JarrettR/USBvil/Firmware/HID/firmware/src/system_config/exp16/dspic33ep256mu506_pim/system.c

/********************************************************************
 Software License Agreement:

 The software supplied herewith by Microchip Technology Incorporated
 (the "Company") for its PIC(R) Microcontroller is intended and
 supplied to you, the Company's customer, for use solely and
 exclusively on Microchip PIC Microcontroller products. The
 software is owned by the Company and/or its supplier, and is
 protected under applicable copyright laws. All rights are reserved.
 Any use in violation of the foregoing restrictions may subject the
 user to criminal sanctions under applicable laws, as well as to
 civil liability for the breach of the terms and conditions of this
 license.

 THIS SOFTWARE IS PROVIDED IN AN "AS IS" CONDITION. NO WARRANTIES,
 WHETHER EXPRESS, IMPLIED OR STATUTORY, INCLUDING, BUT NOT LIMITED
 TO, IMPLIED WARRANTIES OF MERCHANTABILITY AND FITNESS FOR A
 PARTICULAR PURPOSE APPLY TO THIS SOFTWARE. THE COMPANY SHALL NOT,
 IN ANY CIRCUMSTANCES, BE LIABLE FOR SPECIAL, INCIDENTAL OR
 CONSEQUENTIAL DAMAGES, FOR ANY REASON WHATSOEVER.
 *******************************************************************/

#include <p33EP256MU506.h>
#include "system.h"
#include "system_config.h"
#include "usb.h"
#include "leds.h"
#include "buttons.h"
#include "adc.h"

/** CONFIGURATION Bits **********************************************/
// FICD
#pragma config ICS = PGD1               // ICD Communication Channel Select bits (Communicate on PGEC1 and PGED1)
#pragma config JTAGEN = OFF             // JTAG Enable bit (JTAG is disabled)

// FPOR
#pragma config DFMCY = DFMCY_8          // Data Flash Memory Cycle Count (8 Tcy)
#pragma config BOREN = OFF              // Brown Out Reset Enable bit (Brown Out Reset Disabled)
#pragma config ALTI2C1 = OFF            // Alternate I2C1 pins (I2C1 mapped to SDA1/SCL1 pins)
#pragma config ALTI2C2 = OFF            // Alternate I2C2 pins (I2C2 mapped to SDA2/SCL2 pins)
#pragma config WDTWIN = WIN25           // Watchdog Window Select bits (WDT Window is 25% of WDT period)

// FWDT
#pragma config WDTPOST = PS32768        // Watchdog Timer Postscaler bits (1:32,768)
#pragma config WDTPRE = PR128           // Watchdog Timer Prescaler bit (1:128)
#pragma config PLLKEN = ON              // PLL Lock Enable bit (Clock switch to PLL source will wait until the PLL lock signal is valid.)
#pragma config WINDIS = OFF             // Watchdog Timer Window Enable bit (Watchdog Timer in Non-Window mode)
#pragma config FWDTEN = OFF             // Watchdog Timer Enable bit (Watchdog timer enabled/disabled by user software)

// FOSC
#pragma config POSCMD = HS              // Primary Oscillator Mode Select bits (HS Crystal Oscillator Mode)
#pragma config OSCIOFNC = ON            // OSC2 Pin Function bit (OSC2 is general purpose digital I/O pin)
#pragma config IOL1WAY = OFF            // Peripheral pin select configuration (Allow multiple reconfigurations)
#pragma config FCKSM = CSDCMD           // Clock Switching Mode bits (Both Clock switching and Fail-safe Clock Monitor are disabled)

// FOSCSEL
#pragma config FNOSC = PRIPLL           // Oscillator Source Selection (Primary Oscillator with PLL module (XT + PLL, HS + PLL, EC + PLL))
#pragma config PWMLOCK = OFF            // PWM Lock Enable bit (PWM registers may be written without key sequence)
#pragma config IESO = OFF               // Two-speed Oscillator Start-up Enable bit (Start up with user-selected oscillator source)

// FGS
#pragma config GWRP = OFF               // General Segment Write-Protect bit (General Segment may be written)
#pragma config GCP = OFF                // General Segment Code-Protect bit (General Segment Code protect is Disabled)

/*********************************************************************
* Function: void SYSTEM_Initialize( SYSTEM_STATE state )
*
* Overview: Initializes the system.
*
* PreCondition: None
*
* Input:  SYSTEM_STATE - the state to initialize the system into
*
* Output: None
*
********************************************************************/
void SYSTEM_Initialize( SYSTEM_STATE state )
{
    switch(state)
    {
        case SYSTEM_STATE_USB_START:
            ANSELA = 0x0000;
            ANSELB = 0x0000;
            ANSELC = 0x0000;
            ANSELE = 0x0000;
            ANSELG = 0x0000;

            // Configure the device PLL to obtain 60 MIPS operation. The crystal
            // frequency is 8MHz. Divide 8MHz by 2, multiply by 60 and divide by
            // 2. This results in Fosc of 120MHz. The CPU clock frequency is
            // Fcy = Fosc/2 = 60MHz. Wait for the Primary PLL to lock and then
            // configure the auxilliary PLL to provide 48MHz needed for USB
            // Operation.

            PLLFBD = 58;                        /* M  = 60  */
            CLKDIVbits.PLLPOST = 0;             /* N1 = 2   */
            CLKDIVbits.PLLPRE = 0;              /* N2 = 2   */
            OSCTUN = 0;

            /*	Initiate Clock Switch to Primary
             *	Oscillator with PLL (NOSC= 0x3)*/
            __builtin_write_OSCCONH(0x03);
            __builtin_write_OSCCONL(0x01);

            while (OSCCONbits.COSC != 0x3);

            // Configuring the auxiliary PLL, since the primary
            // oscillator provides the source clock to the auxiliary
            // PLL, the auxiliary oscillator is disabled. Note that
            // the AUX PLL is enabled. The input 8MHz clock is divided
            // by 2, multiplied by 24 and then divided by 2. Wait till
            // the AUX PLL locks.

            ACLKCON3 = 0x24C1;
            ACLKDIV3 = 0x7;

            ACLKCON3bits.ENAPLL = 1;
            while(ACLKCON3bits.APLLCK != 1);

            ADC_SetConfiguration(ADC_CONFIGURATION_DEFAULT);
            ADC_ChannelEnable(ADC_CHANNEL_POTENTIOMETER);
            
            LED_Enable(LED_USB_DEVICE_STATE);
            LED_Enable(LED_USB_DEVICE_HID_KEYBOARD_CAPS_LOCK);
            BUTTON_Enable(BUTTON_USB_DEVICE_HID_KEYBOARD_KEY);
            break;

        case SYSTEM_STATE_USB_SUSPEND:
            //If developing a bus powered USB device that needs to be USB compliant,
            //insert code here to reduce the I/O pin and microcontroller power consumption,
            //so that the total current is <2.5mA from the USB host's VBUS supply.
            //If developing a self powered application (or a bus powered device where
            //official USB compliance isn't critical), nothing strictly needs
            //to be done during USB suspend.

            USBSleepOnSuspend();
            break;

        case SYSTEM_STATE_USB_RESUME:
            //Here would be a good place to restore I/O pins and application states
            //back to their original values that may have been saved/changed at the 
            //start of the suspend event (ex: when the SYSTEM_Initialize(SYSTEM_STATE_USB_SUSPEND)
            //callback was called.
            
            //If you didn't change any I/O pin states prior to entry into suspend,
            //then nothing explicitly needs to be done here.  However, by the time
            //the firmware returns from this function, the full application should
            //be restored into effectively exactly the same state as the application
            //was in, prior to entering USB suspend.
            
            //Additionally, before returning from this function, make sure the microcontroller's
            //currently active clock settings are compatible with USB operation, including
            //taking into consideration all possible microcontroller features/effects
            //that can affect the oscillator settings (such as internal/external 
            //switchover (two speed start up), fail-safe clock monitor, PLL lock time,
            //external crystal/resonator startup time (if using a crystal/resonator),
            //etc.

            //Additionally, the official USB specifications dictate that USB devices
            //must become fully operational and ready for new host requests/normal 
            //USB communication after a 10ms "resume recovery interval" has elapsed.
            //In order to meet this timing requirement and avoid possible issues,
            //make sure that all necessary oscillator startup is complete and this
            //function has returned within less than this 10ms interval.

            break;

        default:
            break;
    }
}

#if defined(USB_INTERRUPT)
void __attribute__((interrupt,auto_psv)) _USB1Interrupt()
{
    USBDeviceTasks();
}
#endif


        
