JarrettR/USBvil/Firmware/HID/firmware/src/system_config/exp16/pic24fj128gb204_pim/system.c

/********************************************************************
 Software License Agreement:

 The software supplied herewith by Microchip Technology Incorporated
 (the "Company") for its PIC(R) Microcontroller is intended and
 supplied to you, the Company's customer, for use solely and
 exclusively on Microchip PIC Microcontroller products. The
 software is owned by the Company and/or its supplier, and is
 protected under applicable copyright laws. All rights are reserved.
 Any use in violation of the foregoing restrictions may subject the
 user to criminal sanctions under applicable laws, as well as to
 civil liability for the breach of the terms and conditions of this
 license.

 THIS SOFTWARE IS PROVIDED IN AN "AS IS" CONDITION. NO WARRANTIES,
 WHETHER EXPRESS, IMPLIED OR STATUTORY, INCLUDING, BUT NOT LIMITED
 TO, IMPLIED WARRANTIES OF MERCHANTABILITY AND FITNESS FOR A
 PARTICULAR PURPOSE APPLY TO THIS SOFTWARE. THE COMPANY SHALL NOT,
 IN ANY CIRCUMSTANCES, BE LIABLE FOR SPECIAL, INCIDENTAL OR
 CONSEQUENTIAL DAMAGES, FOR ANY REASON WHATSOEVER.
 *******************************************************************/

#include "system.h"
#include "system_config.h"
#include "usb.h"
#include "leds.h"
#include "buttons.h"
#include "adc.h"

/** CONFIGURATION Bits **********************************************/
// CONFIG1
#pragma config WDTPS = PS32768          // Watchdog Timer Postscaler Select (1:32,768)
#pragma config FWPSA = PR128            // WDT Prescaler Ratio Select (1:128)
#pragma config WINDIS = OFF             // Windowed WDT Disable (Standard Watchdog Timer)
#pragma config FWDTEN = OFF             // Watchdog Timer Enable (WDT disabled in hardware; SWDTEN bit disabled)
#pragma config ICS = PGx1               // Emulator Pin Placement Select bits (Emulator functions are shared with PGEC1/PGED1)
#pragma config LPCFG = OFF              // Low power regulator control (Disabled - regardless of RETEN)
#pragma config GWRP = OFF               // General Segment Write Protect (Write to program memory allowed)
#pragma config GCP = OFF                // General Segment Code Protect (Code protection is disabled)
#pragma config JTAGEN = OFF             // JTAG Port Enable (Disabled)

// CONFIG2
#pragma config POSCMD = HS              // Primary Oscillator Select (HS Oscillator Enabled)
#pragma config WDTCLK = LPRC            // WDT Clock Source Select bits (WDT uses LPRC)
#pragma config OSCIOFCN = ON            // OSCO Pin Configuration (OSCO/CLKO/RA3 functions as port I/O (RA3))
#pragma config FCKSM = CSECMD           // Clock Switching and Fail-Safe Clock Monitor Configuration bits (Clock switching enabled, Fail-Safe Clock Monitor disabled)
#pragma config FNOSC = PRIPLL           // Initial Oscillator Select (Primary Oscillator with PLL module (XTPLL,HSPLL, ECPLL))
#pragma config ALTRB6 = APPEND          // Alternate RB6 pin function enable bit (Append the RP6/ASCL1/PMPD6 functions of RB6 to RA1 pin functions)
#pragma config ALTCMPI = CxINC_RB       // Alternate Comparator Input bit (C1INC is on RB13, C2INC is on RB9 and C3INC is on RA0)
#pragma config WDTCMX = WDTCLK          // WDT Clock Source Select bits (WDT clock source is determined by the WDTCLK Configuration bits)
#pragma config IESO = OFF               // Internal External Switchover (Disabled)

// CONFIG3
#pragma config WPFP = WPFP127           // Write Protection Flash Page Segment Boundary (Page 127 (0x1FC00))
#pragma config SOSCSEL = ON             // SOSC Selection bits (SOSC circuit selected)
#pragma config WDTWIN = PS25_0          // Window Mode Watchdog Timer Window Width Select (Watch Dog Timer Window Width is 25 percent)
#pragma config PLLSS = PLL_FRC          // PLL Secondary Selection Configuration bit (PLL is fed by the FRC oscillator)
#pragma config BOREN = ON               // Brown-out Reset Enable (Brown-out Reset Enabled)
#pragma config WPDIS = WPDIS            // Segment Write Protection Disable (Disabled)
#pragma config WPCFG = WPCFGDIS         // Write Protect Configuration Page Select (Disabled)
#pragma config WPEND = WPENDMEM         // Segment Write Protection End Page Select (Write Protect from WPFP to the last page of memory)

// CONFIG4
#pragma config DSWDTPS = DSWDTPS1F      // Deep Sleep Watchdog Timer Postscale Select bits (1:68719476736 (25.7 Days))
#pragma config DSWDTOSC = LPRC          // DSWDT Reference Clock Select (DSWDT uses LPRC as reference clock)
#pragma config DSBOREN = OFF            // Deep Sleep BOR Enable bit (DSBOR Disabled)
#pragma config DSWDTEN = OFF            // Deep Sleep Watchdog Timer Enable (DSWDT Disabled)
#pragma config DSSWEN = OFF             // DSEN Bit Enable (Deep Sleep operation is always disabled)
#pragma config PLLDIV = DIVIDE2         // USB 96 MHz PLL Prescaler Select bits (Oscillator input divided by 2 (8 MHz input))
#pragma config I2C1SEL = DISABLE        // Alternate I2C1 enable bit (I2C1 uses SCL1 and SDA1 pins)
#pragma config IOL1WAY = OFF            // PPS IOLOCK Set Only Once Enable bit (The IOLOCK bit can be set and cleared using the unlock sequence)

 
/*********************************************************************
* Function: void SYSTEM_Initialize( SYSTEM_STATE state )
*
* Overview: Initializes the system.
*
* PreCondition: None
*
* Input:  SYSTEM_STATE - the state to initialize the system into
*
* Output: None
*
********************************************************************/
void SYSTEM_Initialize( SYSTEM_STATE state )
{
    switch(state)
    {
        case SYSTEM_STATE_USB_START:        
            //Make sure that the general purpose output driver multiplexed with
            //the VBUS pin is always consistently configured to be tri-stated in
            //USB applications, so as to avoid any possible contention with the host.
            //(ex: maintain TRISBbits.TRISB6 = 1 at all times).
            TRISBbits.TRISB6 = 1;
            
            LED_Enable(LED_USB_DEVICE_STATE);
            LED_Enable(LED_USB_DEVICE_HID_KEYBOARD_CAPS_LOCK);
            
            BUTTON_Enable(BUTTON_USB_DEVICE_HID_KEYBOARD_KEY);
            break;
            
        case SYSTEM_STATE_USB_SUSPEND:
            break;

        case SYSTEM_STATE_USB_RESUME:
            break;

        default:
            break;
    }
}

#if defined(USB_INTERRUPT)
void __attribute__((interrupt,auto_psv)) _USB1Interrupt()
{
    USBDeviceTasks();
}
#endif
