JarrettR/USBvil/Firmware/HID/firmware/src/system_config/pic18f_starter_kit/system.c

/********************************************************************
 Software License Agreement:

 The software supplied herewith by Microchip Technology Incorporated
 (the "Company") for its PIC(R) Microcontroller is intended and
 supplied to you, the Company's customer, for use solely and
 exclusively on Microchip PIC Microcontroller products. The
 software is owned by the Company and/or its supplier, and is
 protected under applicable copyright laws. All rights are reserved.
 Any use in violation of the foregoing restrictions may subject the
 user to criminal sanctions under applicable laws, as well as to
 civil liability for the breach of the terms and conditions of this
 license.

 THIS SOFTWARE IS PROVIDED IN AN "AS IS" CONDITION. NO WARRANTIES,
 WHETHER EXPRESS, IMPLIED OR STATUTORY, INCLUDING, BUT NOT LIMITED
 TO, IMPLIED WARRANTIES OF MERCHANTABILITY AND FITNESS FOR A
 PARTICULAR PURPOSE APPLY TO THIS SOFTWARE. THE COMPANY SHALL NOT,
 IN ANY CIRCUMSTANCES, BE LIABLE FOR SPECIAL, INCIDENTAL OR
 CONSEQUENTIAL DAMAGES, FOR ANY REASON WHATSOEVER.
 *******************************************************************/

#include "system.h"
#include "system_config.h"
#include "usb_device.h"

/** CONFIGURATION Bits **********************************************/
 #pragma config WDTEN = OFF          //WDT disabled (enabled by SWDTEN bit)
 #pragma config PLLDIV = 3           //Divide by 3 (12 MHz oscillator input)
 #pragma config STVREN = ON          //stack overflow/underflow reset enabled
 #pragma config XINST = OFF          //Extended instruction set disabled
 #pragma config CPUDIV = OSC1        //No CPU system clock divide
 #pragma config CP0 = OFF            //Program memory is not code-protected
 #pragma config OSC = HSPLL          //HS oscillator, PLL enabled, HSPLL used by USB
 #pragma config FCMEN = OFF          //Fail-Safe Clock Monitor disabled
 #pragma config IESO = OFF           //Two-Speed Start-up disabled
 #pragma config WDTPS = 32768        //1:32768
 #pragma config DSWDTOSC = INTOSCREF //DSWDT uses INTOSC/INTRC as clock
 #pragma config RTCOSC = T1OSCREF    //RTCC uses T1OSC/T1CKI as clock
 #pragma config DSBOREN = OFF        //Zero-Power BOR disabled in Deep Sleep
 #pragma config DSWDTEN = OFF        //Disabled
 #pragma config DSWDTPS = 8192       //1:8,192 (8.5 seconds)
 #pragma config IOL1WAY = OFF        //IOLOCK bit can be set and cleared
 #pragma config MSSP7B_EN = MSK7     //7 Bit address masking
 #pragma config WPFP = PAGE_1        //Write Protect Program Flash Page 0
 #pragma config WPEND = PAGE_0       //Start protection at page 0
 #pragma config WPCFG = OFF          //Write/Erase last page protect Disabled
 #pragma config WPDIS = OFF          //WPFP[5:0], WPEND, and WPCFG bits ignored
 #pragma config T1DIG = ON           //Sec Osc clock source may be selected
 #pragma config LPT1OSC = OFF        //high power Timer1 mode

typedef enum
{
    SOFT_START_POWER_OFF,
    SOFT_START_POWER_START,
    SOFT_START_POWER_ENABLED,
    SOFT_START_POWER_READY
} SOFT_START_STATUS;

static SOFT_START_STATUS softStartStatus = SOFT_START_POWER_OFF;

/*********************************************************************
* Function: void SYSTEM_Initialize( SYSTEM_STATE state )
*
* Overview: Initializes the system.
*
* PreCondition: None
*
* Input:  SYSTEM_STATE - the state to initialize the system into
*
* Output: None
*
********************************************************************/
void SYSTEM_Initialize( SYSTEM_STATE state )
{
    switch(state)
    {
        case SYSTEM_STATE_USB_START:
            //On the PIC18F46J50 Family of USB microcontrollers, the PLL will not power up and be enabled
            //by default, even if a PLL enabled oscillator configuration is selected (such as HS+PLL).
            //This allows the device to power up at a lower initial operating frequency, which can be
            //advantageous when powered from a source which is not gauranteed to be adequate for 48MHz
            //operation.  On these devices, user firmware needs to manually set the OSCTUNE<PLLEN> bit to
            //power up the PLL.
            {
                unsigned int pll_startup_counter = 600;
                OSCTUNEbits.PLLEN = 1;  //Enable the PLL and wait 2+ms until the PLL locks before enabling USB module
                while(pll_startup_counter--);
            }
            //Device switches over automatically to PLL output after PLL is locked and ready.

            
            BUTTON_Enable(BUTTON_USB_DEVICE_HID_KEYBOARD_KEY);
			
            softStartStatus = SOFT_START_POWER_START;
            break;

        case SYSTEM_STATE_USB_SUSPEND: 
            //Configure device for low power consumption.  Turn off app power.
            AppPowerDisable();
            softStartStatus = SOFT_START_POWER_OFF;
            break;
            
        case SYSTEM_STATE_USB_RESUME:
            softStartStatus = SOFT_START_POWER_START;
            break;
    }
}

/*********************************************************************
* Function: void SYSTEM_Tasks(void)
*
* Overview: Runs system level tasks that keep the system running
*
* PreCondition: System has been initalized with SYSTEM_Initialize()
*
* Input: None
*
* Output: None
*
********************************************************************/
void SYSTEM_Tasks(void)
{
    switch(softStartStatus)
    {
        case SOFT_START_POWER_OFF:
            break;

        case SOFT_START_POWER_START:
            if(USBGetDeviceState() != CONFIGURED_STATE)
            {
                break;
            }
            
            AppPowerEnable();
            softStartStatus = SOFT_START_POWER_ENABLED;
            break;

        case SOFT_START_POWER_ENABLED:
            if(AppPowerReady() == true)
            {
                softStartStatus = SOFT_START_POWER_READY;
                LED_Enable(LED_USB_DEVICE_STATE);
                LED_Enable(LED_USB_DEVICE_HID_KEYBOARD_CAPS_LOCK);
				
                ADC_SetConfiguration(ADC_CONFIGURATION_DEFAULT);
                ADC_Enable(ADC_CHANNEL_POTENTIOMETER);
            }
            break;
            
        case SOFT_START_POWER_READY:
            break;
    }
}

			
			
#if defined(__XC8)
void interrupt SYS_InterruptHigh(void)
{
    #if defined(USB_INTERRUPT)
        USBDeviceTasks();
    #endif
}
#endif     
